stevew817/hdmilight-v2/firmware/cmd_output.c

/*

   Copyright (C) 2013 Stephen Robinson
  
   This file is part of HDMI-Light
  
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
*/

#include <inttypes.h>
#include <avr/io.h>
#include <avr/pgmspace.h>
#include <string.h>
#include <stdio.h>
#include "ambilight.h"


void setOutput(uint8_t output, uint16_t light, uint8_t area, uint8_t coef, uint8_t gamma, uint8_t enabled)
{
	//  15    12    9                 0
	// +-+-+-+-+-+-+-+-+-+-+-+-+-+-+-+-+
	// |E| coe  | gam  | area          |
	// +-+-+-+-+-+-+-+-+-+-+-+-+-+-+-+-+
	// |               |               |

	uint8_t* address = AMBILIGHT_BASE_ADDR_OUTPUT;
	address += (uint16_t)output * 1024;
	address += light * 2;

	if(enabled)
		enabled = 0x80;

	address[0] = area & 0xff;
	address[1] = enabled | ((coef & 15) << 3) | (gamma & 7);
}

void getOutput(uint8_t output, uint16_t light, int* area, int* coef, int* gamma, int* enabled)
{
	uint8_t* address = AMBILIGHT_BASE_ADDR_OUTPUT;
	address += (uint16_t)output * 1024;
	address += light * 2;

	*area = address[0];
	*gamma = address[1] & 7;
	*coef = (address[1] >> 3) & 15;
	*enabled = address[1] & 0x80;
}

void cmdSetOutput(uint8_t argc, char** argv)
{
	if(argc == 7)
	{
		int area, coef, gamma, enabled;
		uint8_t output, maxOutput;
		uint8_t light, minLight, maxLight;

		area = getint(&argv[3]);
		coef = getint(&argv[4]);
		gamma = getint(&argv[5]);
		enabled = getint(&argv[6]);
		
		getrange(argv[1], &output, &maxOutput);
		getrange(argv[2], &minLight, &maxLight);
		do
		{
			light = minLight;
			do
			{
				setOutput(output, light, area, coef, gamma, enabled);
				
			} while(light++ < maxLight);
			
		} while(output++ < maxOutput);
	}
}

void cmdGetOutput(uint8_t argc, char** argv)
{
	if(argc == 3)
	{
		uint8_t output, maxOutput;
		uint8_t light, minLight, maxLight;

		getrange(argv[1], &output, &maxOutput);
		getrange(argv[2], &minLight, &maxLight);
		do
		{
			light = minLight;
			do
			{
				int area, coef, gamma, enabled;

				getOutput(output, light, &area, &coef, &gamma, &enabled);

				printf_P(PSTR("%d: %d: %d %d %d %d\n"), output, light, area, coef, gamma, enabled);
				
			} while(light++ < maxLight);
			
		} while(output++ < maxOutput);
	}
}

void cmdRstOutput(uint8_t argc, char** argv)
{
	int output;

	for(output = 0; output < 8; ++output)
	{
		int light;

		for(light = 0; light < 512; ++light)
			setOutput(output, light, light & 0xff, 0, 0, (light & 0x100) == 0);
	}
}
