stevew817/hdmilight-v2/fpga/DCM32to16.vhd

--------------------------------------------------------------------------------
-- Copyright (c) 1995-2009 Xilinx, Inc.  All rights reserved.
--------------------------------------------------------------------------------
--   ____  ____ 
--  /   /\/   / 
-- /___/  \  /    Vendor: Xilinx 
-- \   \   \/     Version : 11.1
--  \   \         Application : xaw2vhdl
--  /   /         Filename : DCM32to16.vhd
-- /___/   /\     Timestamp : 07/29/2010 14:42:37
-- \   \  /  \ 
--  \___\/\___\ 
--
--Command: xaw2vhdl-st C:\dbdev\My Dropbox\GadgetFactory\AVR8\svn\trunk\ipcore_dir\DCM32to16.xaw C:\dbdev\My Dropbox\GadgetFactory\AVR8\svn\trunk\ipcore_dir\DCM32to16
--Design Name: DCM32to16
--Device: xc3s250e-4vq100
--
-- Module DCM32to16
-- Generated by Xilinx Architecture Wizard
-- Written for synthesis tool: XST
-- Period Jitter (unit interval) for block DCM_SP_INST = 0.05 UI
-- Period Jitter (Peak-to-Peak) for block DCM_SP_INST = 3.43 ns

library ieee;
use ieee.std_logic_1164.ALL;
use ieee.numeric_std.ALL;
library UNISIM;
use UNISIM.Vcomponents.ALL;

entity DCM32to16 is
   port ( CLKIN_IN        : in    std_logic; 
          CLKFX_OUT       : out   std_logic; 
          CLKIN_IBUFG_OUT : out   std_logic; 
          CLK0_OUT        : out   std_logic);
end DCM32to16;

architecture BEHAVIORAL of DCM32to16 is
   signal CLKFB_IN        : std_logic;
   signal CLKFX_BUF       : std_logic;
   signal CLKIN_IBUFG     : std_logic;
   signal CLK0_BUF        : std_logic;
   signal GND_BIT         : std_logic;
begin
   GND_BIT <= '0';
   CLKIN_IBUFG_OUT <= CLKIN_IBUFG;
   CLK0_OUT <= CLKFB_IN;
   CLKFX_BUFG_INST : BUFG
      port map (I=>CLKFX_BUF,
                O=>CLKFX_OUT);
   
   CLKIN_IBUFG_INST : IBUFG
      port map (I=>CLKIN_IN,
                O=>CLKIN_IBUFG);
   
   CLK0_BUFG_INST : BUFG
      port map (I=>CLK0_BUF,
                O=>CLKFB_IN);
   
   DCM_SP_INST : DCM_SP
   generic map( CLK_FEEDBACK => "1X",
            CLKDV_DIVIDE => 2.0,
            CLKFX_DIVIDE => 32,
            CLKFX_MULTIPLY => 16,
            CLKIN_DIVIDE_BY_2 => FALSE,
            CLKIN_PERIOD => 31.250,
            CLKOUT_PHASE_SHIFT => "NONE",
            DESKEW_ADJUST => "SYSTEM_SYNCHRONOUS",
            DFS_FREQUENCY_MODE => "LOW",
            DLL_FREQUENCY_MODE => "LOW",
            DUTY_CYCLE_CORRECTION => TRUE,
            FACTORY_JF => x"C080",
            PHASE_SHIFT => 0,
            STARTUP_WAIT => FALSE)
      port map (CLKFB=>CLKFB_IN,
                CLKIN=>CLKIN_IBUFG,
                DSSEN=>GND_BIT,
                PSCLK=>GND_BIT,
                PSEN=>GND_BIT,
                PSINCDEC=>GND_BIT,
                RST=>GND_BIT,
                CLKDV=>open,
                CLKFX=>CLKFX_BUF,
                CLKFX180=>open,
                CLK0=>CLK0_BUF,
                CLK2X=>open,
                CLK2X180=>open,
                CLK90=>open,
                CLK180=>open,
                CLK270=>open,
                LOCKED=>open,
                PSDONE=>open,
                STATUS=>open);
   
end BEHAVIORAL;
