stevew817/hdmilight-v2/firmware/cmd_area.c

/*

   Copyright (C) 2013 Stephen Robinson
  
   This file is part of HDMI-Light
  
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
*/

#include <inttypes.h>
#include <avr/io.h>
#include <avr/pgmspace.h>
#include <string.h>
#include <stdio.h>
#include "ambilight.h"


void setArea(unsigned int area, 
             unsigned char xmin, unsigned char xmax,
             unsigned char ymin, unsigned char ymax,
             unsigned char shift)
{
	uint8_t* address = AMBILIGHT_BASE_ADDR_AREA;
	address += (uint16_t)area * 4;

	//  31      28      24          18          12          6           0
	// +-+-+-+-+-+-+-+-+-+-+-+-+-+-+-+-+-+-+-+-+-+-+-+-+-+-+-+-+-+-+-+-+-+
	// | unused  | shift | ymax      | ymin      | xmax      | xmin      |
	// +-+-+-+-+-+-+-+-+-+-+-+-+-+-+-+-+-+-+-+-+-+-+-+-+-+-+-+-+-+-+-+-+-+
	// |                 |               |               |               |

	area <<= 2;
	address[0] = (xmin & 0x3f) | (xmax << 6);
	address[1] = ((xmax & 0x3f) >> 2) | (ymin << 4);
	address[2] = ((ymin & 0x3f) >> 4) | (ymax << 2);
	address[3] = shift & 0xf;
}

void cmdSetArea(uint8_t argc, char** argv)
{
	if(argc == 7)
	{
		uint8_t index, maxIndex;
		uint8_t xmin, xmax, ymin, ymax, shift;
		
		xmin = getint(&argv[2]);
		xmax = getint(&argv[3]);
		ymin = getint(&argv[4]);
		ymax = getint(&argv[5]);
		shift = getint(&argv[6]);

		getrange(argv[1], &index, &maxIndex);
		do
		{
			setArea(index, xmin, xmax, ymin, ymax, shift);

		} while(index++ < maxIndex);
	}
}

void cmdGetArea(uint8_t argc, char** argv)
{
	if(argc == 2)
	{
		uint8_t index, maxIndex;

		getrange(argv[1], &index, &maxIndex);
		do
		{
			uint8_t* address = AMBILIGHT_BASE_ADDR_AREA + ((uint16_t)index * 4);
			int x;

			x = address[0] & 0x3f; // xmin
			printf_P(PSTR("%d: %d "), index, x);
			x = (address[0] >> 6) | ((address[1] & 0x0f) << 2); // xmax
			printf_P(PSTR("%d "), x);
			x = (address[1] >> 4) | ((address[2] & 3) << 4); // ymin
			printf_P(PSTR("%d "), x);
			x = (address[2] >> 2); // ymax
			printf_P(PSTR("%d "), x);
			x = address[3] & 0xf; // shift
			printf_P(PSTR("%d "), x);

		} while(index++ < maxIndex);
	}
}

void cmdRstArea(uint8_t argc, char** argv)
{
	int i;

	for(i = 0; i < 64; ++i)
		setArea(i, i, i, 0, 8, 3);
}
